emeb/spi_fiend/firmware/common/spi.h

/*
 * spi.h - spi driver for F042_usb_spi
 * 01-23-2019 E. Brombaugh
 */

#ifndef __spi__
#define __spi__

#include "stm32f0xx.h"

void spi_init(void);
uint32_t spi_send_data(uint8_t *data, uint32_t sz);
uint8_t spi_config_start(void);
uint8_t spi_config_finish(void);
uint8_t spi_get_flash_id(uint8_t *data);
uint8_t spi_flash_erase(uint32_t addr);
uint8_t spi_flash_read_start(uint32_t addr);
uint8_t spi_flash_read_data(uint8_t *buf, uint32_t len);
uint8_t spi_flash_read_finish(void);
uint8_t spi_flash_write_start(uint32_t addr, uint32_t len);
uint8_t spi_flash_write_data(uint8_t *buf, uint32_t len);

#endif
